OLIMEX/GateMateA1-EVB/HARDWARE/GateMateA1-EVB-Rev.C/GateMateA1-EVB_Rev_C.kicad_sch

## KiCad design HARDWARE/GateMateA1-EVB-Rev.C/GateMateA1-EVB_Rev_C.kicad_sch (2025-12-08)

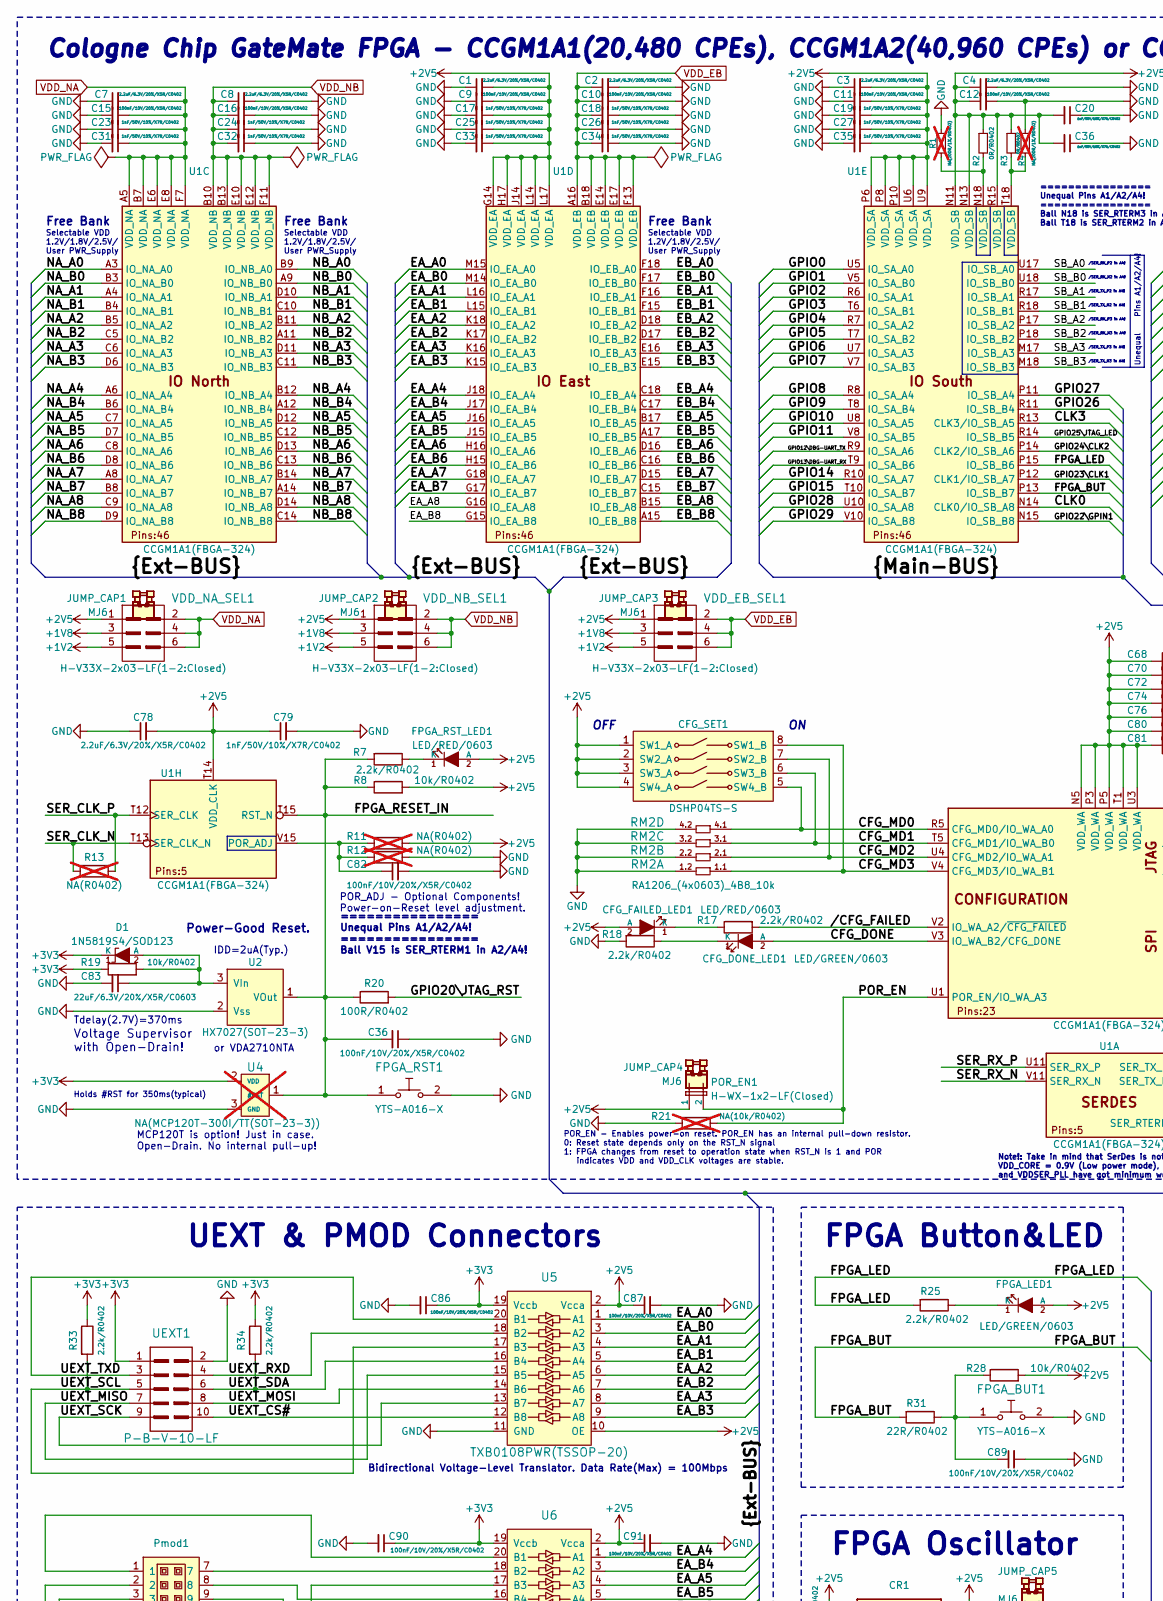
[picture p9: schematic GateMateA1-EVB_Rev_C.kicad_sch, part in row 1, column 1]

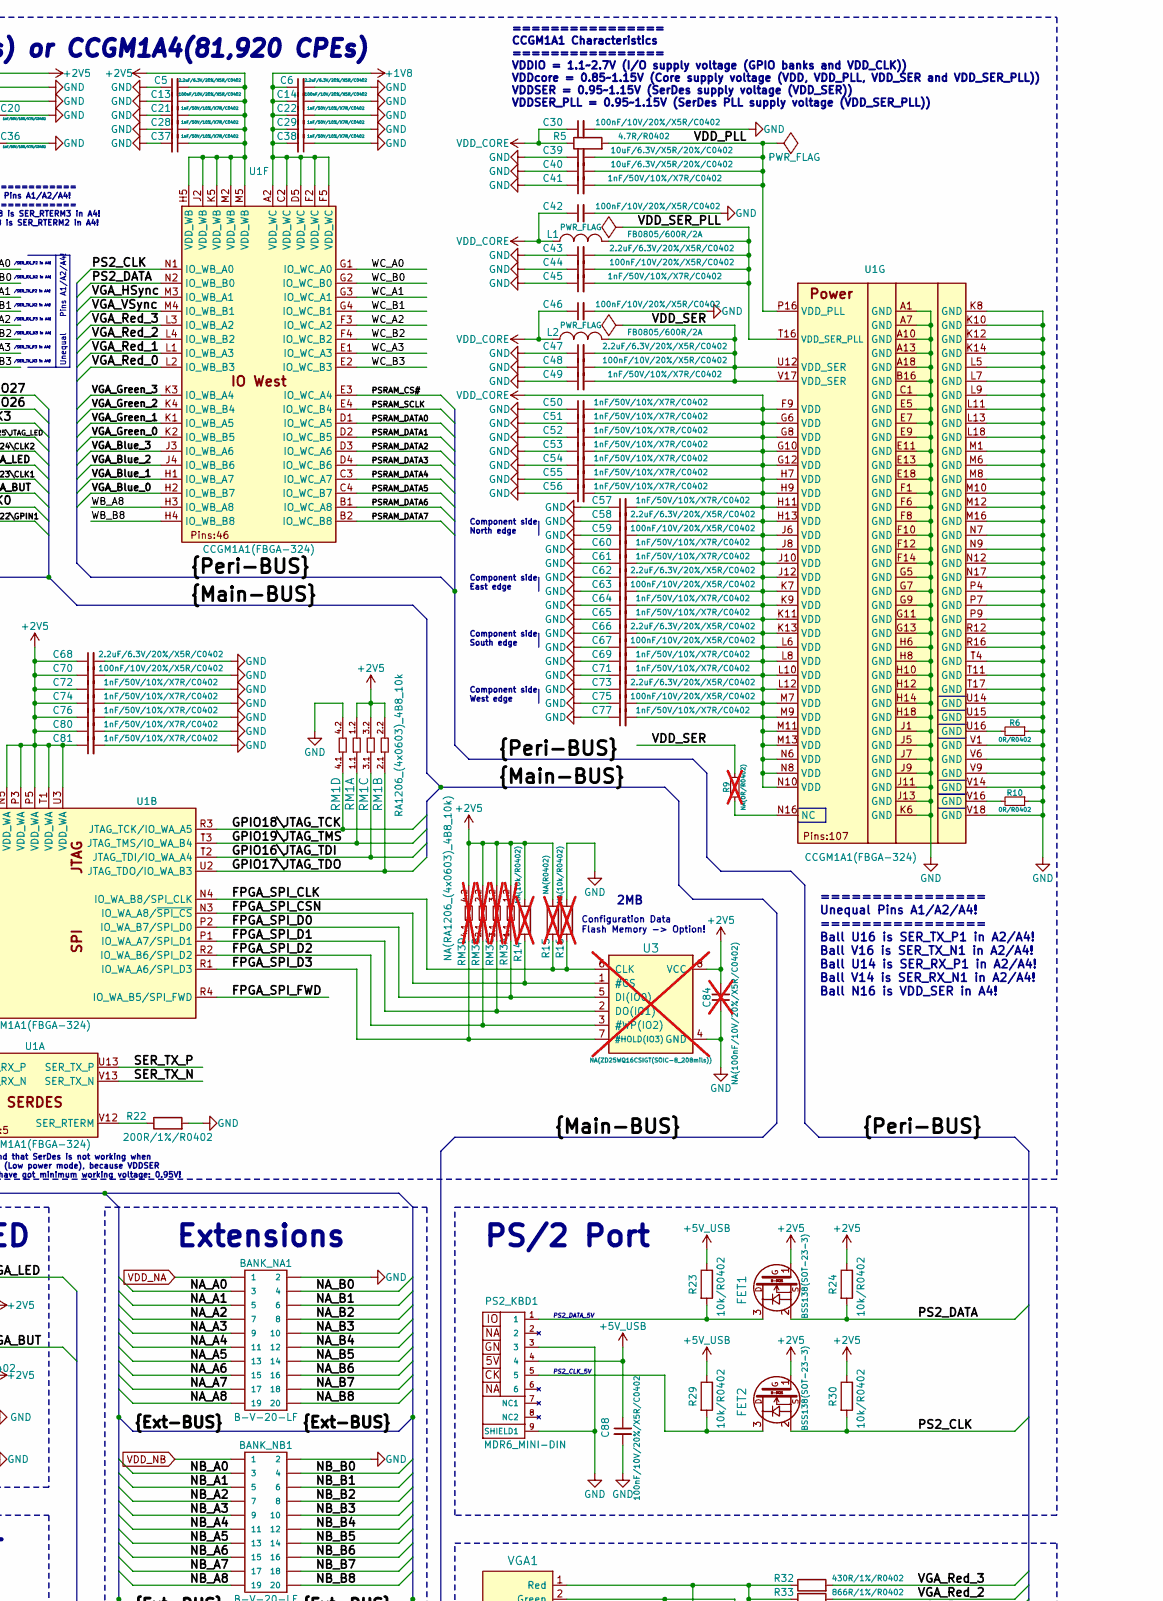
[picture p10: schematic GateMateA1-EVB_Rev_C.kicad_sch, part in row 1, column 2]

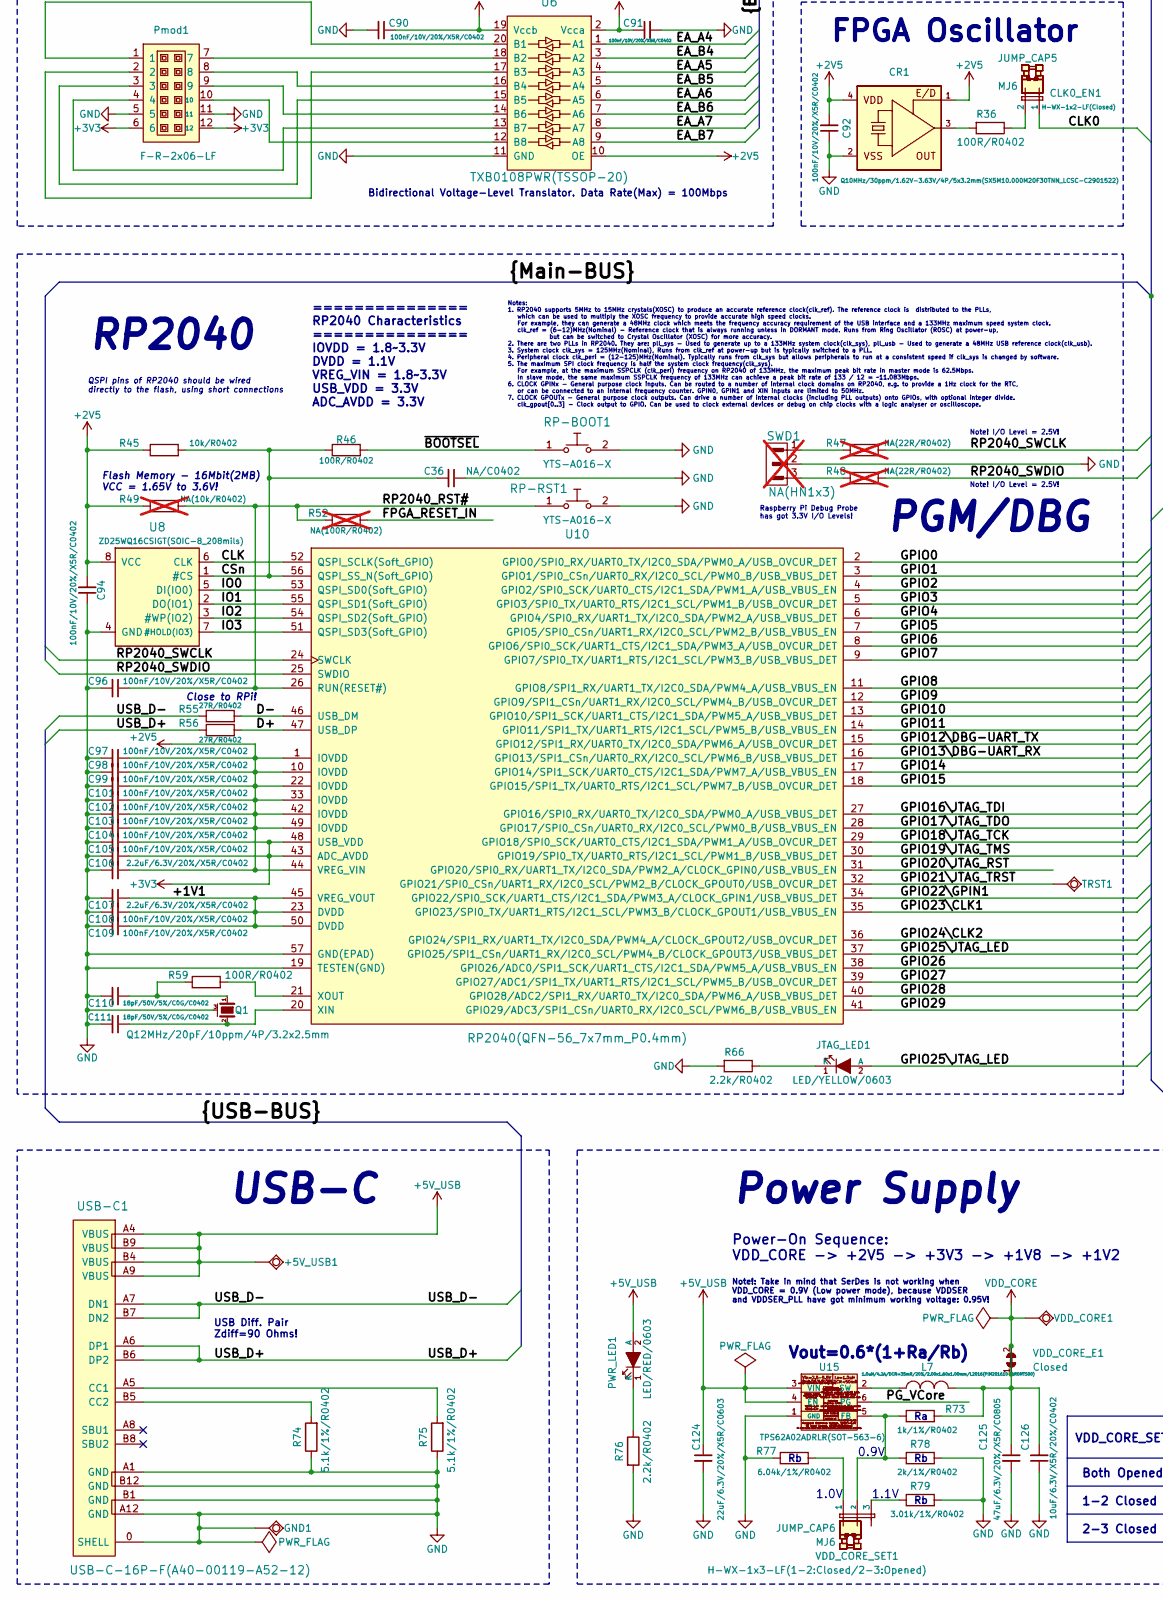
[picture p11: schematic GateMateA1-EVB_Rev_C.kicad_sch, part in row 2, column 1]

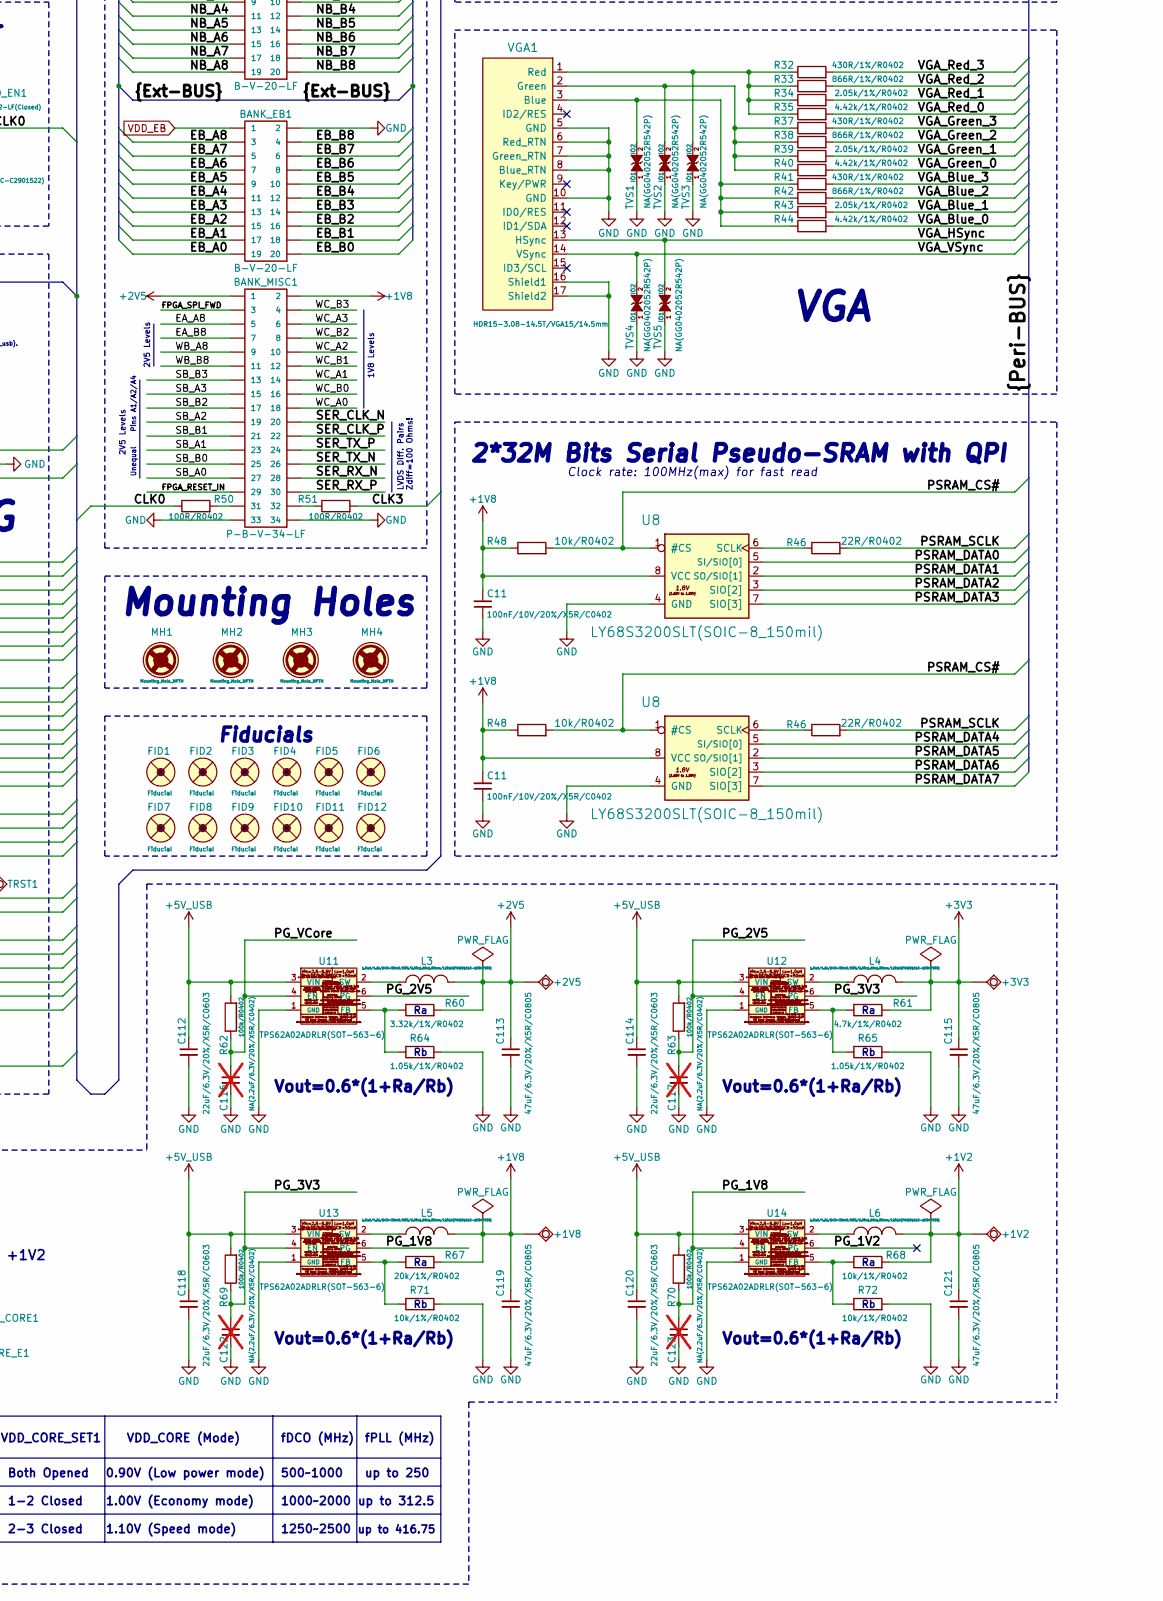
[picture p12: schematic GateMateA1-EVB_Rev_C.kicad_sch, part in row 2, column 2]

Parts:
+1V2, +1V8, +2V5, +3V3, +5V_USB1: TESTPAD; TEST_PAD_40x70_Round
BANK_EB1: B-V-20-LF; GBH-254-SMT-20
BANK_MISC1: P-B-V-34-LF; GBH-254-SMT-34
BANK_NA1: B-V-20-LF; GBH-254-SMT-20
BANK_NB1: B-V-20-LF; GBH-254-SMT-20
C1, C2, C3, C4, C5, C6, C7, C8, C43, C47, C58, C62, C66, C68, C73, C78, C106, C107: 2.2uF/6.3V/20%/X5R/C0402; C_0402_5MIL_DWS
C9, C10, C11, C12, C13, C14, C15, C16, C30, C42, C44, C46, C48, C59, C63, C67, C70, C75, C82, C86, C87, C88, C89, C90, C91, C92, C94, C96, C97, C98, C99, C101, C102, C103, C104, C105, C108, C109: 100nF/10V/20%/X5R/C0402; C_0402_5MIL_DWS
C17, C18, C19, C20, C21, C22, C23, C24, C25, C26, C27, C28, C29, C31, C32, C33, C34, C35, C36, C37, C38, C41, C45, C49, C50, C51, C52, C53, C54, C55, C56, C57, C60, C61, C64, C65, C69, C71, C72, C74, C76, C77, C79, C80, C81: 1nF/50V/10%/X7R/C0402; C_0402_5MIL_DWS
C39, C40, C126: 10uF/6.3V/X5R/20%/C0402; C_0402_5MIL_DWS
C83, C112, C114, C118, C120, C124: 22uF/6.3V/20%/X5R/C0603; C_0603_5MIL_DWS
C84: NA(100nF/10V/20%/X5R/C0402); C_0402_5MIL_DWS; not fitted
C110, C111: 18pF/50V/5%/C0G/C0402; C_0402_5MIL_DWS
C113, C115, C119, C121, C125: 47uF/6.3V/20%/X5R/C0805; C_0805_5MIL_DWS
C116, C117, C122, C123: NA(2.2uF/6.3V/20%/X5R/C0402); C_0402_5MIL_DWS; not fitted
CFG_DONE_LED1: LED/GREEN/0603; LED_0603_KA
CFG_FAILED_LED1: LED/RED/0603; LED_0603_KA
CFG_SET1: DSHP04TS-S; DSHP04TS-S-1.27mm_Half_4_Slide
CLK0_EN1: H-WX-1x2-LF(Closed); HN1x2(SMD)_H-WX-1x2-LF
CR1: Q10MHz/30ppm/1.62V-3.63V/4P/5x3.2mm(SX5M10.000M20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; 5032-4P_HCX-3S
D1: 1N5819S4/SOD123; SOD-123_1C-2A_KA
FET1, FET2: BSS138(SOT-23-3); SOT23
FID1, FID2, FID3, FID7, FID8, FID9: Fiducial; Fiducial1x3
FID4, FID5, FID6, FID10, FID11, FID12: Fiducial; Fiducial1x3_Paste
FPGA_BUT1: YTS-A016-X
FPGA_LED1: LED/GREEN/0603; LED_0603_KA
FPGA_RST1: YTS-A016-X
FPGA_RST_LED1: LED/RED/0603; LED_0603_KA
GND1: TESTPAD; TEST_PAD_40x70_Round
JTAG_LED1: LED/YELLOW/0603; LED_0603_KA
JUMP_CAP1, JUMP_CAP2, JUMP_CAP3, JUMP_CAP4, JUMP_CAP5, JUMP_CAP6: MJ6
L1, L2: FB0805/600R/2A; L_0805_5MIL_DWS
L3, L4, L5, L6, L7: 1.0uH/4.2A/DCR=35mR/20%/2.00x1.60x1.00mm/L2016(PI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; L_2016_MM
MH1, MH2, MH3, MH4: Mounting_Hole_NPTH; Mounting_Hole_Drill-3.3mm_Clerance-7mm
POR_EN1: H-WX-1x2-LF(Closed); HN1x2(SMD)_H-WX-1x2-LF
PS2_KBD1: MDR6_MINI-DIN; PS2_MDR6_MINI-DIN
PWR_LED1: LED/RED/0603; LED_0603_KA
Pmod1: F-R-2x06-LF; Digilent_Pmod_12-pin
Q1: Q12MHz/20pF/10ppm/4P/3.2x2.5mm; TSX-3.2x2.5mm_GND(3)
R1, R4: NA(200R/1%/R0402); R_0402_5MIL_DWS; not fitted
R2, R3, R6, R10: 0R/R0402; R_0402_5MIL_DWS
R5: 4.7R/R0402; R_0402_5MIL_DWS
R7, R17, R18, R25, R66, R76: 2.2k/R0402; R_0402_5MIL_DWS
R8, R19, R23, R24, R28, R29, R30, R45, R48: 10k/R0402; R_0402_5MIL_DWS
R9: NA(0R/R0402); R_0402_5MIL_DWS; not fitted
R11, R12, R13, R15: NA(R0402); R_0402_5MIL_DWS; not fitted
R14, R16, R21, R49: NA(10k/R0402); R_0402_5MIL_DWS; not fitted
R20, R36, R46, R50, R51, R59: 100R/R0402; R_0402_5MIL_DWS
R22: 200R/1%/R0402; R_0402_5MIL_DWS
R31: 22R/R0402; R_0402_5MIL_DWS
R32, R37, R41: 430R/1%/R0402; R_0402_5MIL_DWS
R33, R38, R42: 866R/1%/R0402; R_0402_5MIL_DWS
R34, R39, R43: 2.05k/1%/R0402; R_0402_5MIL_DWS
R35, R40, R44: 4.42k/1%/R0402; R_0402_5MIL_DWS
R47: NA(22R/R0402); R_0402_5MIL_DWS; not fitted
R52: NA(100R/R0402); R_0402_5MIL_DWS; not fitted
R55, R56: 27R/R0402; R_0402_5MIL_DWS
R60: 3.32k/1%/R0402; R_0402_5MIL_DWS
R61: 4.7k/1%/R0402; R_0402_5MIL_DWS
R62, R63, R69, R70: 100k/R0402; R_0402_5MIL_DWS
R64, R65: 1.05k/1%/R0402; R_0402_5MIL_DWS
R67: 20k/1%/R0402; R_0402_5MIL_DWS
R68, R71, R72: 10k/1%/R0402; R_0402_5MIL_DWS
R73: 1k/1%/R0402; R_0402_5MIL_DWS
R74, R75: 5.1k/1%/R0402; R_0402_5MIL_DWS
R77: 6.04k/1%/R0402; R_0402_5MIL_DWS
R78: 2k/1%/R0402; R_0402_5MIL_DWS
R79: 3.01k/1%/R0402; R_0402_5MIL_DWS
RM1, RM2: RA1206_(4x0603)_4B8_10k; RA1206_(4X0603)_4B8_xx
RM3: NA(RA1206_(4x0603)_4B8_10k); RA1206_(4X0603)_4B8_xx; not fitted
RP-BOOT1: YTS-A016-X
RP-RST1: YTS-A016-X
SWD1: NA(HN1x3); HN1x3; not fitted
TRST1: TESTPAD; TEST_PAD_40x70_Round
TVS1, TVS2, TVS3, TVS4, TVS5: NA(GG0402052R542P); D_0402_5MIL_DWS
U1: CCGM1A1(FBGA-324); FBGA-324_P0.8mm_Pad0.4mm_Ball0.45mm_Dim15.00x15.00x1.20mm
U2: HX7027(SOT-23-3); SOT-23
U3: NA(ZD25WQ16CSIGT(SOIC-8_208mils)); SO-8_208mil; not fitted
U4: NA(MCP120T-300I/TT(SOT-23-3)); SOT-23; not fitted
U5, U6: TXB0108PWR(TSSOP-20); TSSOP20_Pitch-0.65mm_6.6x4.5x1.2mm
U8: LY68S3200SLT(SOIC-8_150mil); SOIC-8_150mil
U10: RP2040(QFN-56_7x7mm_P0.4mm); QFN56_7x7_Pitch_0.4mm
U11, U12, U13, U14, U15: TPS62A02ADRLR(SOT-563-6); SOT-563-6
UEXT1: P-B-V-10-LF; GBH-254-SMT-10
USB-C1: USB-C-16P-F(A40-00119-A52-12); USB2.0_TYPE-C(A40-00119-A52-12)_Paste
VDD_CORE1: TESTPAD; TEST_PAD_40x70_Round
VDD_CORE_E1: Closed; SJ_Closed
VDD_CORE_SET1: H-WX-1x3-LF(1-2:Closed/2-3:Opened); HN1x3(SMD)_H-WX-1x3-LF
VDD_EB_SEL1: H-V33X-2x03-LF(1-2:Closed); GPH254SMT02x03(H-V33X-2X3-LF)
VDD_NA_SEL1: H-V33X-2x03-LF(1-2:Closed); GPH254SMT02x03(H-V33X-2X3-LF)
VDD_NB_SEL1: H-V33X-2x03-LF(1-2:Closed); GPH254SMT02x03(H-V33X-2X3-LF)
VGA1: HDR15-3.08-14.5T/VGA15/14.5mm; VGA15-F(HDR15-3.08-14.5T)_DrillSlot

Connections:
+1V1: C107.1, C108.1, C109.1, U10.23 (DVDD), U10.45 (VREG_VOUT), U10.50 (DVDD)
+1V2: +1V2.1, C121.1, L6.2, R68.2, VDD_EB_SEL1.5, VDD_NA_SEL1.5, VDD_NB_SEL1.5
+1V8: +1V8.1, BANK_MISC1.2, C6.1, C11.2, C14.1, C22.2, C29.2, C38.2, C119.1, L5.2, R48.1, R67.2, U1.A2 (VDD_WC), U1.C2 (VDD_WC), U1.D5 (VDD_WC), U1.F2 (VDD_WC), U1.F5 (VDD_WC), U8.8 (VCC), VDD_EB_SEL1.3, VDD_NA_SEL1.3, VDD_NB_SEL1.3
+2V5: +2V5.1, BANK_MISC1.1, C1.2, C3.2, C4.1, C5.2, C9.1, C11.1, C12.1, C13.1, C17.1, C19.1, C20.2, C21.1, C25.1, C27.1, C28.1, C33.1, C35.1, C36.2, C37.1, C68.1, C70.1, C72.1, C74.1, C76.1, C78.2, C79.1, C80.1, C81.1, C84.2, C87.1, C91.1, C92.2, C94.2, C97.1, C98.1, C99.1, C101.1, C102.1, C103.1, C106.1, C113.1, CFG_FAILED_LED1.2 (A), CFG_SET1.1 (SW1_A), CFG_SET1.2 (SW2_A), CFG_SET1.3 (SW3_A), CFG_SET1.4 (SW4_A), CR1.1 (E/D), CR1.4 (VDD), FET1.1 (G), FET2.1 (G), FPGA_LED1.2 (A), FPGA_RST_LED1.2 (A), L3.2, POR_EN1.1, R2.1, R3.1, R8.2, R11.2, R14.2, R15.2, R24.1, R28.2, R30.1, R45.1, R49.1, R60.2, RM1.1.2, RM1.2.2, RM1.3.2, RM3.1.2, RM3.2.2, RM3.3.2, RM3.4.2, U1.G14 (VDD_EA), U1.H5 (VDD_WB), U1.H17 (VDD_EA), U1.J2 (VDD_WB), U1.J14 (VDD_EA), U1.K5 (VDD_WB), U1.L14 (VDD_EA), U1.L17 (VDD_EA), U1.M2 (VDD_WB), U1.M5 (VDD_WB), U1.N5 (VDD_WA), U1.N11 (VDD_SB), U1.N13 (VDD_SB), U1.P3 (VDD_WA), U1.P5 (VDD_WA), U1.P6 (VDD_SA), U1.P8 (VDD_SA), U1.P10 (VDD_SA), U1.R15 (VDD_SB), U1.T1 (VDD_WA), U1.T14 (VDD_CLK), U1.U3 (VDD_WA), U1.U6 (VDD_SA), U1.U9 (VDD_SA), U3.8 (VCC), U5.2 (Vcca), U5.10 (OE), U6.2 (Vcca), U6.10 (OE), U8.8 (VCC), U10.1 (IOVDD), U10.10 (IOVDD), U10.22 (IOVDD), U10.33 (IOVDD), U10.42 (IOVDD), U10.44 (VREG_VIN), U10.49 (IOVDD), VDD_EB_SEL1.1, VDD_NA_SEL1.1, VDD_NB_SEL1.1
+3V3: +3V3.1, C86.1, C90.1, C104.1, C105.1, C115.1, D1.1 (K), L4.2, Pmod1.6, Pmod1.12, R19.1, R33.1, R34.1, R61.2, U4.2 (VDD), U5.19 (Vccb), U6.19 (Vccb), U10.43 (ADC_AVDD), U10.48 (USB_VDD), UEXT1.1
+5V_USB: +5V_USB1.1, C88.1, C112.1, C114.1, C118.1, C120.1, C124.1, PS2_KBD1.4, PWR_LED1.2 (A), R23.1, R29.1, R62.2, R63.2, R69.2, R70.2, U11.3 (VIN), U12.3 (VIN), U13.3 (VIN), U14.3 (VIN), U15.3 (VIN), U15.4 (EN), USB-C1.A4 (VBUS), USB-C1.A9 (VBUS), USB-C1.B4 (VBUS), USB-C1.B9 (VBUS)
CFG_DONE: CFG_DONE_LED1.2 (A), U1.V3 (IO_WA_B2/CFG_DONE)
CFG_MD0: CFG_SET1.5 (SW4_B), RM2.4.1, U1.R5 (CFG_MD0/IO_WA_A0)
CFG_MD1: CFG_SET1.6 (SW3_B), RM2.3.1, U1.T5 (CFG_MD1/IO_WA_B0)
CFG_MD2: CFG_SET1.7 (SW2_B), RM2.2.1, U1.U4 (CFG_MD2/IO_WA_A1)
CFG_MD3: CFG_SET1.8 (SW1_B), RM2.1.1, U1.V4 (CFG_MD3/IO_WA_B1)
CLK: U8.6 (CLK), U10.52 (QSPI_SCLK(Soft_GPIO))
CLK0: CLK0_EN1.1, R50.1, U1.N14 (CLK0/IO_SB_A8)
CLK3: R51.2, U1.R13 (CLK3/IO_SB_A5)
CSn: C36.2, R45.2, R46.1, U8.1 (#CS), U10.56 (QSPI_SS_N(Soft_GPIO))
D+: R56.2, U10.47 (USB_DP)
D-: R55.2, U10.46 (USB_DM)
EA_A0: U1.M15 (IO_EA_A0), U5.1 (A1)
EA_A1: U1.L16 (IO_EA_A1), U5.4 (A3)
EA_A2: U1.K18 (IO_EA_A2), U5.6 (A5)
EA_A3: U1.K16 (IO_EA_A3), U5.8 (A7)
EA_A4: U1.J18 (IO_EA_A4), U6.1 (A1)
EA_A5: U1.J16 (IO_EA_A5), U6.4 (A3)
EA_A6: U1.H16 (IO_EA_A6), U6.6 (A5)
EA_A7: U1.G18 (IO_EA_A7), U6.8 (A7)
EA_A8: BANK_MISC1.5, U1.G16 (IO_EA_A8)
EA_B0: U1.M14 (IO_EA_B0), U5.3 (A2)
EA_B1: U1.L15 (IO_EA_B1), U5.5 (A4)
EA_B2: U1.K17 (IO_EA_B2), U5.7 (A6)
EA_B3: U1.K15 (IO_EA_B3), U5.9 (A8)
EA_B4: U1.J17 (IO_EA_B4), U6.3 (A2)
EA_B5: U1.J15 (IO_EA_B5), U6.5 (A4)
EA_B6: U1.H15 (IO_EA_B6), U6.7 (A6)
EA_B7: U1.G17 (IO_EA_B7), U6.9 (A8)
EA_B8: BANK_MISC1.7, U1.G15 (IO_EA_B8)
EB_A0: BANK_EB1.19, U1.F18 (IO_EB_A0)
EB_A1: BANK_EB1.17, U1.F16 (IO_EB_A1)
EB_A2: BANK_EB1.15, U1.D18 (IO_EB_A2)
EB_A3: BANK_EB1.13, U1.E16 (IO_EB_A3)
EB_A4: BANK_EB1.11, U1.C18 (IO_EB_A4)
EB_A5: BANK_EB1.9, U1.B17 (IO_EB_A5)
EB_A6: BANK_EB1.7, U1.D16 (IO_EB_A6)
EB_A7: BANK_EB1.5, U1.D15 (IO_EB_A7)
EB_A8: BANK_EB1.3, U1.B15 (IO_EB_A8)
EB_B0: BANK_EB1.20, U1.F17 (IO_EB_B0)
EB_B1: BANK_EB1.18, U1.F15 (IO_EB_B1)
EB_B2: BANK_EB1.16, U1.D17 (IO_EB_B2)
EB_B3: BANK_EB1.14, U1.E15 (IO_EB_B3)
EB_B4: BANK_EB1.12, U1.C17 (IO_EB_B4)
EB_B5: BANK_EB1.10, U1.A17 (IO_EB_B5)
EB_B6: BANK_EB1.8, U1.C16 (IO_EB_B6)
EB_B7: BANK_EB1.6, U1.C15 (IO_EB_B7)
EB_B8: BANK_EB1.4, U1.A15 (IO_EB_B8)
FPGA_BUT: R31.2, U1.P13 (IO_SB_B7)
FPGA_LED: R25.2, U1.P15 (IO_SB_B6)
FPGA_RESET_IN: BANK_MISC1.29, C36.2, FPGA_RST1.1, R7.2, R8.1, R20.1, R52.2, U1.T15 (RST_N), U2.1 (VOut), U4.1 (#RST)
FPGA_SPI_CLK: R15.1, R16.1, U1.N4 (IO_WA_B8/SPI_CLK), U3.6 (CLK)
FPGA_SPI_CSN: R14.1, U1.N3 (IO_WA_A8/~SPI_CS), U3.1 (#CS)
FPGA_SPI_D0: RM3.1.1, U1.P2 (IO_WA_B7/SPI_D0), U3.5 (DI(IO0))
FPGA_SPI_D1: RM3.3.1, U1.P1 (IO_WA_A7/SPI_D1), U3.2 (DO(IO1))
FPGA_SPI_D2: RM3.2.1, U1.R2 (IO_WA_B6/SPI_D2), U3.3 (#WP(IO2))
FPGA_SPI_D3: RM3.4.1, U1.R1 (IO_WA_A6/SPI_D3), U3.7 (#HOLD(IO3))
FPGA_SPI_FWD: BANK_MISC1.3, U1.R4 (IO_WA_B5/SPI_FWD)
GND: BANK_EB1.2, BANK_MISC1.33, BANK_MISC1.34, BANK_NA1.2, BANK_NB1.2, C1.1, C2.2, C3.1, C4.2, C5.1, C6.2, C7.1, C8.2, C9.2, C10.2, C11.1, C11.2, C12.2, C13.2, C14.2, C15.2, C16.1, C17.2, C18.1, C19.2, C20.1, C21.2, C22.1, C23.2, C24.1, C25.2, C26.1, C27.2, C28.2, C29.1, C30.2, C31.2, C32.1, C33.2, C34.1, C35.2, C36.1, C37.2, C38.1, C39.1, C40.1, C41.1, C42.2, C43.1, C44.1, C45.1, C46.2, C47.1, C48.1, C49.1, C50.1, C51.1, C52.1, C53.1, C54.1, C55.1, C56.1, C57.1, C58.1, C59.1, C60.1, C61.1, C62.1, C63.1, C64.1, C65.1, C66.1, C67.1, C68.2, C69.1, C70.2, C71.1, C72.2, C73.1, C74.2, C75.1, C76.2, C77.1, C78.1, C79.2, C80.2, C81.2, C82.2, C83.2, C84.1, C86.2, C87.2, C88.2, C89.2, C90.2, C91.2, C92.1, C94.1, C96.2, C97.2, C98.2, C99.2, C101.2, C102.2, C103.2, C104.2, C105.2, C106.2, C107.2, C108.2, C109.2, C110.2, C111.2, C112.2, C113.2, C114.2, C115.2, C116.2, C117.2, C118.2, C119.2, C120.2, C121.2, C122.2, C123.2, C124.2, C125.2, C126.1, CR1.2 (VSS), FPGA_BUT1.2, FPGA_RST1.2, GND1.1, PS2_KBD1.3, PS2_KBD1.9 (SHIELD1), Pmod1.5, Pmod1.11, Q1.3 (case), R1.1, R4.1, R6.1, R10.1, R12.2, R16.2, R18.2, R21.1, R22.2, R64.2, R65.2, R66.2, R71.2, R72.2, R74.1, R75.1, R76.2, R77.1, R78.2, R79.2, RM1.4.2, RM2.1.2, RM2.2.2, RM2.3.2, RM2.4.2, RP-BOOT1.2, RP-RST1.2, SWD1.2, TVS1.1 (IO1), TVS2.1 (IO1), TVS3.1 (IO1), TVS4.1 (IO1), TVS5.1 (IO1), U1.A1 (GND), U1.A7 (GND), U1.A10 (GND), U1.A13 (GND), U1.A18 (GND), U1.B16 (GND), U1.C1 (GND), U1.E5 (GND), U1.E7 (GND), U1.E9 (GND), U1.E11 (GND), U1.E13 (GND), U1.E18 (GND), U1.F1 (GND), U1.F6 (GND), U1.F8 (GND), U1.F10 (GND), U1.F12 (GND), U1.F14 (GND), U1.G5 (GND), U1.G7 (GND), U1.G9 (GND), U1.G11 (GND), U1.G13 (GND), U1.H6 (GND), U1.H8 (GND), U1.H10 (GND), U1.H12 (GND), U1.H14 (GND), U1.H18 (GND), U1.J1 (GND), U1.J5 (GND), U1.J7 (GND), U1.J9 (GND), U1.J11 (GND), U1.J13 (GND), U1.K6 (GND), U1.K8 (GND), U1.K10 (GND), U1.K12 (GND), U1.K14 (GND), U1.L5 (GND), U1.L7 (GND), U1.L9 (GND), U1.L11 (GND), U1.L13 (GND), U1.L18 (GND), U1.M1 (GND), U1.M6 (GND), U1.M8 (GND), U1.M10 (GND), U1.M12 (GND), U1.M16 (GND), U1.N7 (GND), U1.N9 (GND), U1.N12 (GND), U1.N17 (GND), U1.P4 (GND), U1.P7 (GND), U1.P9 (GND), U1.R12 (GND), U1.R16 (GND), U1.T4 (GND), U1.T11 (GND), U1.T17 (GND), U1.U14 (GND), U1.U15 (GND), U1.V1 (GND), U1.V6 (GND), U1.V9 (GND), U1.V14 (GND), U1.V18 (GND), U2.2 (Vss), U3.4 (GND), U4.3 (GND), U5.11 (GND), U6.11 (GND), U8.4 (GND), U10.19 (TESTEN(GND)), U10.57 (GND(EPAD)), U11.1 (GND), U12.1 (GND), U13.1 (GND), U14.1 (GND), U15.1 (GND), UEXT1.2, USB-C1.0 (SHELL), USB-C1.A1 (GND), USB-C1.A12 (GND), USB-C1.B1 (GND), USB-C1.B12 (GND), VGA1.5 (GND), VGA1.6 (Red_RTN), VGA1.7 (Green_RTN), VGA1.8 (Blue_RTN), VGA1.10 (GND), VGA1.16 (Shield1), VGA1.17 (Shield2)
GPIO0: U1.U5 (IO_SA_A0), U10.2 (GPIO0/SPI0_RX/UART0_TX/I2C0_SDA/PWM0_A/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)
GPIO1: U1.V5 (IO_SA_B0), U10.3 (GPIO1/SPI0_CSn/UART0_RX/I2C0_SCL/PWM0_B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)
GPIO2: U1.R6 (IO_SA_A1), U10.4 (GPIO2/SPI0_SCK/UART0_CTS/I2C1_SDA/PWM1_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)
GPIO3: U1.T6 (IO_SA_B1), U10.5 (GPIO3/SPI0_TX/UART0_RTS/I2C1_SCL/PWM1_B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)
GPIO4: U1.R7 (IO_SA_A2), U10.6 (GPIO4/SPI0_RX/UART1_TX/I2C0_SDA/PWM2_A/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)
GPIO5: U1.T7 (IO_SA_B2), U10.7 (GPIO5/SPI0_CSn/UART1_RX/I2C0_SCL/PWM2_B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)
GPIO6: U1.U7 (IO_SA_A3), U10.8 (GPIO6/SPI0_SCK/UART1_CTS/I2C1_SDA/PWM3_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)
GPIO7: U1.V7 (IO_SA_B3), U10.9 (GPIO7/SPI0_TX/UART1_RTS/I2C1_SCL/PWM3_B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)
GPIO8: U1.R8 (IO_SA_A4), U10.11 (GPIO8/SPI1_RX/UART1_TX/I2C0_SDA/PWM4_A/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)
GPIO9: U1.T8 (IO_SA_B4), U10.12 (GPIO9/SPI1_CSn/UART1_RX/I2C0_SCL/PWM4_B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)
GPIO10: U1.U8 (IO_SA_A5), U10.13 (GPIO10/SPI1_SCK/UART1_CTS/I2C1_SDA/PWM5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)
GPIO11: U1.V8 (IO_SA_B5), U10.14 (GPIO11/SPI1_TX/UART1_RTS/I2C1_SCL/PWM5_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)
GPIO12\DBG-UART_TX: U1.R9 (IO_SA_A6), U10.15 (GPIO12/SPI1_RX/UART0_TX/I2C0_SDA/PWM6_A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)
GPIO13\DBG-UART_RX: U1.T9 (IO_SA_B6), U10.16 (GPIO13/SPI1_CSn/UART0_RX/I2C0_SCL/PWM6_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)
GPIO14: U1.R10 (IO_SA_A7), U10.17 (GPIO14/SPI1_SCK/UART0_CTS/I2C1_SDA/PWM7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)
GPIO15: U1.T10 (IO_SA_B7), U10.18 (GPIO15/SPI1_TX/UART0_RTS/I2C1_SCL/PWM7_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)
GPIO16\JTAG_TDI: RM1.3.1, U1.T2 (JTAG_TDI/IO_WA_A4), U10.27 (GPIO16/SPI0_RX/UART0_TX/I2C0_SDA/PWM0_A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)
GPIO17\JTAG_TDO: RM1.2.1, U1.U2 (JTAG_TDO/IO_WA_B3), U10.28 (GPIO17/SPI0_CSn/UART0_RX/I2C0_SCL/PWM0_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)
GPIO18\JTAG_TCK: RM1.4.1, U1.R3 (JTAG_TCK/IO_WA_A5), U10.29 (GPIO18/SPI0_SCK/UART0_CTS/I2C1_SDA/PWM1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)
GPIO19\JTAG_TMS: RM1.1.1, U1.T3 (JTAG_TMS/IO_WA_B4), U10.30 (GPIO19/SPI0_TX/UART0_RTS/I2C1_SCL/PWM1_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)
GPIO20\JTAG_RST: R20.2, U10.31 (GPIO20/SPI0_RX/UART1_TX/I2C0_SDA/PWM2_A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)
GPIO21\JTAG_TRST: TRST1.1, U10.32 (GPIO21/SPI0_CSn/UART1_RX/I2C0_SCL/PWM2_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)
GPIO22\GPIN1: U1.N15 (IO_SB_B8), U10.34 (GPIO22/SPI0_SCK/UART1_CTS/I2C1_SDA/PWM3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)
GPIO23\CLK1: U1.P12 (CLK1/IO_SB_A7), U10.35 (GPIO23/SPI0_TX/UART1_RTS/I2C1_SCL/PWM3_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)
GPIO24\CLK2: U1.P14 (CLK2/IO_SB_A6), U10.36 (GPIO24/SPI1_RX/UART1_TX/I2C0_SDA/PWM4_A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)
GPIO25\JTAG_LED: JTAG_LED1.2 (A), U1.R14 (IO_SB_B5), U10.37 (GPIO25/SPI1_CSn/UART1_RX/I2C0_SCL/PWM4_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)
GPIO26: U1.R11 (IO_SB_B4), U10.38 (GPIO26/ADC0/SPI1_SCK/UART1_CTS/I2C1_SDA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)
GPIO27: U1.P11 (IO_SB_A4), U10.39 (GPIO27/ADC1/SPI1_TX/UART1_RTS/I2C1_SCL/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)
GPIO28: U1.U10 (IO_SA_A8), U10.40 (GPIO28/ADC2/SPI1_RX/UART0_TX/I2C0_SDA/P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)
GPIO29: U1.V10 (IO_SA_B8), U10.41 (GPIO29/ADC3/SPI1_CSn/UART0_RX/I2C0_SCL/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)
IO0: U8.5 (DI(IO0)), U10.53 (QSPI_SD0(Soft_GPIO))
IO1: U8.2 (DO(IO1)), U10.55 (QSPI_SD1(Soft_GPIO))
IO2: U8.3 (#WP(IO2)), U10.54 (QSPI_SD2(Soft_GPIO))
IO3: U8.7 (#HOLD(IO3)), U10.51 (QSPI_SD3(Soft_GPIO))
NA_A0: BANK_NA1.3, U1.A3 (IO_NA_A0)
NA_A1: BANK_NA1.5, U1.A4 (IO_NA_A1)
NA_A2: BANK_NA1.7, U1.B5 (IO_NA_A2)
NA_A3: BANK_NA1.9, U1.C6 (IO_NA_A3)
NA_A4: BANK_NA1.11, U1.A6 (IO_NA_A4)
NA_A5: BANK_NA1.13, U1.C7 (IO_NA_A5)
NA_A6: BANK_NA1.15, U1.C8 (IO_NA_A6)
NA_A7: BANK_NA1.17, U1.A8 (IO_NA_A7)
NA_A8: BANK_NA1.19, U1.C9 (IO_NA_A8)
NA_B0: BANK_NA1.4, U1.B3 (IO_NA_B0)
NA_B1: BANK_NA1.6, U1.B4 (IO_NA_B1)
NA_B2: BANK_NA1.8, U1.C5 (IO_NA_B2)
NA_B3: BANK_NA1.10, U1.D6 (IO_NA_B3)
NA_B4: BANK_NA1.12, U1.B6 (IO_NA_B4)
NA_B5: BANK_NA1.14, U1.D7 (IO_NA_B5)
NA_B6: BANK_NA1.16, U1.D8 (IO_NA_B6)
NA_B7: BANK_NA1.18, U1.B8 (IO_NA_B7)
NA_B8: BANK_NA1.20, U1.D9 (IO_NA_B8)
NB_A0: BANK_NB1.3, U1.B9 (IO_NB_A0)
NB_A1: BANK_NB1.5, U1.D10 (IO_NB_A1)
NB_A2: BANK_NB1.7, U1.B11 (IO_NB_A2)
NB_A3: BANK_NB1.9, U1.D11 (IO_NB_A3)
NB_A4: BANK_NB1.11, U1.B12 (IO_NB_A4)
NB_A5: BANK_NB1.13, U1.D12 (IO_NB_A5)
NB_A6: BANK_NB1.15, U1.D13 (IO_NB_A6)
NB_A7: BANK_NB1.17, U1.B14 (IO_NB_A7)
NB_A8: BANK_NB1.19, U1.D14 (IO_NB_A8)
NB_B0: BANK_NB1.4, U1.A9 (IO_NB_B0)
NB_B1: BANK_NB1.6, U1.C10 (IO_NB_B1)
NB_B2: BANK_NB1.8, U1.A11 (IO_NB_B2)
NB_B3: BANK_NB1.10, U1.C11 (IO_NB_B3)
NB_B4: BANK_NB1.12, U1.A12 (IO_NB_B4)
NB_B5: BANK_NB1.14, U1.C12 (IO_NB_B5)
NB_B6: BANK_NB1.16, U1.C13 (IO_NB_B6)
NB_B7: BANK_NB1.18, U1.A14 (IO_NB_B7)
NB_B8: BANK_NB1.20, U1.C14 (IO_NB_B8)
unnamed: BANK_MISC1.31, R50.2
unnamed: BANK_MISC1.32, R51.1
unnamed: C82.1, R11.1, R12.1, U1.V15 (POR_ADJ)
unnamed: C83.1, D1.2 (A), R19.2, U2.3 (VIn)
unnamed: C89.1, FPGA_BUT1.1, R28.1, R31.1
unnamed: C110.1, Q1.1, R59.1
unnamed: C111.1, Q1.2, U10.20 (XIN)
unnamed: CFG_DONE_LED1.1 (K), R18.1
unnamed: CFG_FAILED_LED1.1 (K), R17.1
unnamed: CLK0_EN1.2, R36.1
unnamed: CR1.3 (OUT), R36.2
unnamed: FET1.3 (D), PS2_KBD1.1, R23.2
unnamed: FET2.3 (D), PS2_KBD1.5, R29.2
unnamed: FPGA_LED1.1 (K), R25.1
unnamed: FPGA_RST_LED1.1 (K), R7.1
unnamed: JTAG_LED1.1 (K), R66.1
unnamed: L3.1, U11.2 (SW)
unnamed: L4.1, U12.2 (SW)
unnamed: L5.1, U13.2 (SW)
unnamed: L6.1, U14.2 (SW)
unnamed: L7.1, U15.2 (SW)
unnamed: PWR_LED1.1 (K), R76.1
unnamed: Pmod1.1, U6.20 (B1)
unnamed: Pmod1.2, U6.17 (B3)
unnamed: Pmod1.3, U6.15 (B5)
unnamed: Pmod1.4, U6.13 (B7)
unnamed: Pmod1.7, U6.18 (B2)
unnamed: Pmod1.8, U6.16 (B4)
unnamed: Pmod1.9, U6.14 (B6)
unnamed: Pmod1.10, U6.12 (B8)
unnamed: R1.2, R2.2, U1.N18 (VDD_SB)
unnamed: R3.2, R4.2, U1.T18 (VDD_SB)
unnamed: R6.2, U1.U16 (GND)
unnamed: R9.2, U1.N16 (NC)
unnamed: R10.2, U1.V16 (GND)
unnamed: R22.1, U1.V12 (SER_RTERM)
unnamed: R32.1, R33.1, R34.1, R35.1, TVS3.2 (IO2), VGA1.1 (Red)
unnamed: R37.1, R38.1, R39.1, R40.1, TVS2.2 (IO2), VGA1.2 (Green)
unnamed: R41.1, R42.1, R43.1, R44.1, TVS1.2 (IO2), VGA1.3 (Blue)
unnamed: R46.1, U8.6 (CLK)
unnamed: R47.2, SWD1.1
unnamed: R48.2, SWD1.3
unnamed: R59.2, U10.21 (XOUT)
unnamed: R60.1, R64.1, U11.5 (FB)
unnamed: R61.1, R65.1, U12.5 (FB)
unnamed: R67.1, R71.1, U13.5 (FB)
unnamed: R68.1, R72.1, U14.5 (FB)
unnamed: R73.1, R78.1, U15.5 (FB), VDD_CORE_SET1.2
unnamed: R74.2, USB-C1.B5 (CC2)
unnamed: R75.2, USB-C1.A5 (CC1)
unnamed: R77.2, VDD_CORE_SET1.1
unnamed: R79.1, VDD_CORE_SET1.3
PG_1V2: U14.6 (PG)
PG_1V8: C123.1, R70.1, U13.6 (PG), U14.4 (EN)
PG_2V5: C117.1, R63.1, U11.6 (PG), U12.4 (EN)
PG_3V3: C122.1, R69.1, U12.6 (PG), U13.4 (EN)
PG_VCore: C116.1, R62.1, U11.4 (EN), U15.6 (PG)
POR_EN: POR_EN1.2, R21.2, U1.U1 (POR_EN/IO_WA_A3)
PS2_CLK: FET2.2 (S), R30.2, U1.N1 (IO_WB_A0)
PS2_DATA: FET1.2 (S), R24.2, U1.N2 (IO_WB_B0)
PSRAM_CS#: R48.2, U1.E3 (IO_WC_A4), U8.1 (#CS)
PSRAM_DATA0: U1.D1 (IO_WC_A5), U8.5 (DI(IO0))
PSRAM_DATA1: U1.D2 (IO_WC_B5), U8.2 (DO(IO1))
PSRAM_DATA2: U1.D3 (IO_WC_A6), U8.3 (#WP(IO2))
PSRAM_DATA3: U1.D4 (IO_WC_B6), U8.7 (#HOLD(IO3))
PSRAM_DATA4: U1.C3 (IO_WC_A7), U8.5 (DI(IO0))
PSRAM_DATA5: U1.C4 (IO_WC_B7), U8.2 (DO(IO1))
PSRAM_DATA6: U1.B1 (IO_WC_A8), U8.3 (#WP(IO2))
PSRAM_DATA7: U1.B2 (IO_WC_B8), U8.7 (#HOLD(IO3))
PSRAM_SCLK: R46.2, U1.E4 (IO_WC_B4)
RP2040_RST#: C96.1, R49.2, R52.1, RP-RST1.1, U10.26 (RUN(RESET#))
RP2040_SWCLK: R47.1, U10.24 (SWCLK)
RP2040_SWDIO: R48.1, U10.25 (SWDIO)
SB_A0: BANK_MISC1.27, U1.U17 (IO_SB_A0)
SB_A1: BANK_MISC1.23, U1.R17 (IO_SB_A1)
SB_A2: BANK_MISC1.19, U1.P17 (IO_SB_A2)
SB_A3: BANK_MISC1.15, U1.M17 (IO_SB_A3)
SB_B0: BANK_MISC1.25, U1.U18 (IO_SB_B0)
SB_B1: BANK_MISC1.21, U1.R18 (IO_SB_B1)
SB_B2: BANK_MISC1.17, U1.P18 (IO_SB_B2)
SB_B3: BANK_MISC1.13, U1.M18 (IO_SB_B3)
SER_CLK_N: BANK_MISC1.20, R13.1, U1.T13 (SER_CLK_N)
SER_CLK_P: BANK_MISC1.22, R13.2, U1.T12 (SER_CLK)
SER_RX_N: BANK_MISC1.28, U1.V11 (SER_RX_N)
SER_RX_P: BANK_MISC1.30, U1.U11 (SER_RX_P)
SER_TX_N: BANK_MISC1.26, U1.V13 (SER_TX_N)
SER_TX_P: BANK_MISC1.24, U1.U13 (SER_TX_P)
UEXT_CS#: U5.12 (B8), UEXT1.10
UEXT_MISO: U5.15 (B5), UEXT1.7
UEXT_MOSI: U5.14 (B6), UEXT1.8
UEXT_RXD: U5.18 (B2), UEXT1.4
UEXT_SCK: U5.13 (B7), UEXT1.9
UEXT_SCL: R33.2, U5.17 (B3), UEXT1.5
UEXT_SDA: R34.2, U5.16 (B4), UEXT1.6
UEXT_TXD: U5.20 (B1), UEXT1.3
USB_D+: R56.1, USB-C1.A6 (DP1), USB-C1.B6 (DP2)
USB_D-: R55.1, USB-C1.A7 (DN1), USB-C1.B7 (DN2)
VDD_CORE: C30.1, C42.1, C46.1, C50.2, C51.2, C52.2, C53.2, C54.2, C55.2, C56.2, C57.2, C58.2, C59.2, C60.2, C61.2, C62.2, C63.2, C64.2, C65.2, C66.2, C67.2, C69.2, C71.2, C73.2, C75.2, C77.2, C125.1, C126.2, L1.1, L2.1, L7.2, R5.1, R73.2, U1.F9 (VDD), U1.G6 (VDD), U1.G8 (VDD), U1.G10 (VDD), U1.G12 (VDD), U1.H7 (VDD), U1.H9 (VDD), U1.H11 (VDD), U1.H13 (VDD), U1.J6 (VDD), U1.J8 (VDD), U1.J10 (VDD), U1.J12 (VDD), U1.K7 (VDD), U1.K9 (VDD), U1.K11 (VDD), U1.K13 (VDD), U1.L6 (VDD), U1.L8 (VDD), U1.L10 (VDD), U1.L12 (VDD), U1.M7 (VDD), U1.M9 (VDD), U1.M11 (VDD), U1.M13 (VDD), U1.N6 (VDD), U1.N8 (VDD), U1.N10 (VDD), VDD_CORE1.1, VDD_CORE_E1.1, VDD_CORE_E1.2
VDD_EB: BANK_EB1.1, C2.1, C10.1, C18.2, C26.2, C34.2, U1.A16 (VDD_EB), U1.B18 (VDD_EB), U1.E14 (VDD_EB), U1.E17 (VDD_EB), U1.F13 (VDD_EB), VDD_EB_SEL1.2, VDD_EB_SEL1.4, VDD_EB_SEL1.6
VDD_NA: BANK_NA1.1, C7.2, C15.1, C23.1, C31.1, U1.A5 (VDD_NA), U1.B7 (VDD_NA), U1.E6 (VDD_NA), U1.E8 (VDD_NA), U1.F7 (VDD_NA), VDD_NA_SEL1.2, VDD_NA_SEL1.4, VDD_NA_SEL1.6
VDD_NB: BANK_NB1.1, C8.1, C16.2, C24.2, C32.2, U1.B10 (VDD_NB), U1.B13 (VDD_NB), U1.E10 (VDD_NB), U1.E12 (VDD_NB), U1.F11 (VDD_NB), VDD_NB_SEL1.2, VDD_NB_SEL1.4, VDD_NB_SEL1.6
VDD_PLL: C39.2, C40.2, C41.2, R5.2, U1.P16 (VDD_PLL)
VDD_SER: C47.2, C48.2, C49.2, L2.2, R9.1, U1.U12 (VDD_SER), U1.V17 (VDD_SER)
VDD_SER_PLL: C43.2, C44.2, C45.2, L1.2, U1.T16 (VDD_SER_PLL)
VGA_Blue_0: R44.2, U1.H2 (IO_WB_B7)
VGA_Blue_1: R43.2, U1.H1 (IO_WB_A7)
VGA_Blue_2: R42.2, U1.J4 (IO_WB_B6)
VGA_Blue_3: R41.2, U1.J3 (IO_WB_A6)
VGA_Green_0: R40.2, U1.K2 (IO_WB_B5)
VGA_Green_1: R39.2, U1.K1 (IO_WB_A5)
VGA_Green_2: R38.2, U1.K4 (IO_WB_B4)
VGA_Green_3: R37.2, U1.K3 (IO_WB_A4)
VGA_HSync: TVS5.2 (IO2), U1.M3 (IO_WB_A1), VGA1.13 (HSync)
VGA_Red_0: R35.2, U1.L2 (IO_WB_B3)
VGA_Red_1: R34.2, U1.L1 (IO_WB_A3)
VGA_Red_2: R33.2, U1.L4 (IO_WB_B2)
VGA_Red_3: R32.2, U1.L3 (IO_WB_A2)
VGA_VSync: TVS4.2 (IO2), U1.M4 (IO_WB_B1), VGA1.14 (VSync)
WB_A8: BANK_MISC1.9, U1.H3 (IO_WB_A8)
WB_B8: BANK_MISC1.11, U1.H4 (IO_WB_B8)
WC_A0: BANK_MISC1.18, U1.G1 (IO_WC_A0)
WC_A1: BANK_MISC1.14, U1.G3 (IO_WC_A1)
WC_A2: BANK_MISC1.10, U1.F3 (IO_WC_A2)
WC_A3: BANK_MISC1.6, U1.E1 (IO_WC_A3)
WC_B0: BANK_MISC1.16, U1.G2 (IO_WC_B0)
WC_B1: BANK_MISC1.12, U1.G4 (IO_WC_B1)
WC_B2: BANK_MISC1.8, U1.F4 (IO_WC_B2)
WC_B3: BANK_MISC1.4, U1.E2 (IO_WC_B3)
/CFG_FAILED: R17.2, U1.V2 (IO_WA_A2/~CFG_FAILED)
~BOOTSEL: R46.2, RP-BOOT1.1

Notes on the sheet:
Vout=0.6*(1+Ra/Rb)
USB Diff. Pair Zdiff=90 Ohms!
1-2 Closed
up to 250
/SER_TX_P2 in A4!
QSPI pins of RP2040 should be wired directly to the flash, using short connections
Note!: Take in mind that SerDes is not working when VDD_CORE = 0.9V (Low power mode), because VDDSER and VDDSER_PLL have got minimum working voltage: 0.95V!
Both Opened
Free Bank
Raspberry Pi Debug Probe has got 3.3V I/O Levels!
Close to RPi!
1.10V (Speed mode)
/SER_TX_P3 in A4!
Note! I/O Level = 2.5V!
Unequal Pins A1/A2/A4
0.9V
or VDA2710NTA
2V5 Levels
500~1000
/SER_TX_N3 in A4!
Power-Good Reset.
Extensions
up to 416.75
1000~2000
Power Supply
================ Unequal Pins A1/A2/A4! ================ Ball N18 is SER_RTERM3 in A4! Ball T18 is SER_RTERM2 in A4!
================ Unequal Pins A1/A2/A4! ================ Ball V15 is SER_RTERM1 in A2/A4!
1.0V
FPGA Button&LED
OFF
Selectable VDD 1.2V/1.8V/2.5V/ User PWR_Supply
up to 312.5
Power-On Sequence: VDD_CORE -> +2V5 -> +3V3 -> +1V8 -> +1V2
POR_ADJ - Optional Components! Power-on-Reset level adjustment.
fDCO (MHz)
UEXT & PMOD Connectors
PS/2 Port
1.00V (Economy mode)
VGA
Tdelay(2.7V)=370ms
Fiducials
RP2040
Clock rate: 100MHz(max) for fast read
/SER_RX_P3 in A4!
Mounting Holes
IDD=2uA(Typ.)
fPLL (MHz)
Component side West edge
=============== RP2040 Characteristics =============== IOVDD = 1.8~3.3V DVDD = 1.1V VREG_VIN = 1.8~3.3V USB_VDD = 3.3V ADC_AVDD = 3.3V
2MB
Holds #RST for 350ms(typical)
Notes: 1. RP2040 supports 5MHz to 15MHz crystals(XOSC) to produce an accurate reference clock(clk_ref). The reference clock is distributed to the PLLs, which can be used to multiply the XOSC frequency to provide accurate high speed clocks. For example, they can generate a 48MHz clock which meets th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
2*32M Bits Serial Pseudo-SRAM with QPI
1V8 Levels
Cologne Chip GateMate FPGA - CCGM1A1(20,480 CPEs), CCGM1A2(40,960 CPEs) or CCGM1A4(81,920 CPEs)
MCP120T is option! Just in case. Open-Drain. No internal pull-up!
/SER_TX_N2 in A4!
PGM/DBG
Bidirectional Voltage-Level Translator. Data Rate(Max) = 100Mbps
1250~2500
USB-C
Unequal Pins A1/A2/A4!
FPGA Oscillator
Component side North edge
PS2_DATA_5V
Voltage Supervisor with Open-Drain!
Component side East edge
PS2_CLK_5V
================ Unequal Pins A1/A2/A4! ================ Ball U16 is SER_TX_P1 in A2/A4! Ball V16 is SER_TX_N1 in A2/A4! Ball U14 is SER_RX_P1 in A2/A4! Ball V14 is SER_RX_N1 in A2/A4! Ball N16 is VDD_SER in A4!
0.90V (Low power mode)
Component side South edge
/SER_RX_P2 in A4!
POR_EN - Enables power-on reset. POR_EN has an internal pull-down resistor. 0: Reset state depends only on the RST_N signal 1: FPGA changes from reset to operation state when RST_N is 1 and POR indicates VDD and VDD_CLK voltages are stable.
VDD_CORE (Mode)
/SER_RX_N3 in A4!
Flash Memory - 16Mbit(2MB) VCC = 1.65V to 3.6V!
Configuration Data Flash Memory -> Option!
LVDS Diff. Pairs Zdiff=100 Ohms!
================ CCGM1A1 Characteristics ================ VDDIO = 1.1~2.7V (I/O supply voltage (GPIO banks and VDD_CLK)) VDDcore = 0.85~1.15V (Core supply voltage (VDD, VDD_PLL, VDD_SER and VDD_SER_PLL)) VDDSER = 0.95~1.15V (SerDes supply voltage (VDD_SER)) VDDSER_PLL = 0.95~1.15V (SerDes PLL suppl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
/SER_RX_N2 in A4!
1.1V
2-3 Closed
VDD_CORE_SET1
